KLelong/smartmeter-p1-v1/Software/sm-serial.h

/*
 * sm-serial.h
 * 
 * module to read Smartmeter data from serial port
 */
 
int FindCharInArrayRev(char array[], char c, int len) {
  for (int i = len - 1; i >= 0; i--) {
    if (array[i] == c) {
      return i;
    }
  }
  return -1;
}

long getValidVal(long valNew, long valOld, long maxDiffer)
{
  //check if the incoming value is valid
      if(valOld > 0 && ((valNew - valOld > maxDiffer) && (valOld - valNew > maxDiffer)))
        return valOld;
      return valNew;
}

bool isNumber(char* res, int len) {
  for (int i = 0; i < len; i++) {
    if (((res[i] < '0') || (res[i] > '9'))  && (res[i] != '.' && res[i] != 0)) {
      return false;
    }
  }
  return true;
} 

float getGasValue(char* buffer, int maxlen) {
  int s = FindCharInArrayRev(buffer, '(', maxlen - 2);
  if (s < 8) return 0;
  if (s > 32) s = 32;
  int l = FindCharInArrayRev(buffer, '*', maxlen - 2) - s - 1;
  if (l < 4) return 0;
  if (l > 12) return 0;
  char res[16];
  memset(res, 0, sizeof(res));

  if (strncpy(res, buffer + s + 1, l)) {
    if (isNumber(res, l)) {
      return (atof(res));
    }
  }
  return 0;
}

long getValue(char* buffer, int maxlen) {
  int s = FindCharInArrayRev(buffer, '(', maxlen - 2);
  if (s < 8) return 0;
  if (s > 32) s = 32;
  int l = FindCharInArrayRev(buffer, '*', maxlen - 2) - s - 1;
  if (l < 4) return 0;
  if (l > 12) return 0;
  char res[16];
  memset(res, 0, sizeof(res));

  if (strncpy(res, buffer + s + 1, l)) {
    if (isNumber(res, l)) {
      return (1000 * atof(res));
    }
  }
  return 0;
}

bool decodeTelegram(int len) {
  //need to check for start
  int startChar = FindCharInArrayRev(telegram, '/', len);
  int endChar = FindCharInArrayRev(telegram, '!', len);
  bool endOfMessage = false;
  if(startChar>=0)
  {
    if(outputOnSerial)
    {
      for(int cnt=startChar; cnt<len-startChar;cnt++)
        Serial.print(telegram[cnt]);
    }
  }
  else if(endChar>=0)
  {
    endOfMessage = true;
    if(outputOnSerial)
    {
      for(int cnt=0; cnt<len;cnt++)
        Serial.print(telegram[cnt]);
    }
  }
  else
  {
    if(outputOnSerial)
    {
      for(int cnt=0; cnt<len;cnt++)
        Serial.print(telegram[cnt]);
    }
  }

  long val =0;
  long val2=0;
  // 1-0:1.8.1(000992.992*kWh)
  // 1-0:1.8.1 = Elektra verbruik dag tarief (DSMR v4.0)
  if (strncmp(telegram, "1-0:1.8.1", strlen("1-0:1.8.1")) == 0)
    powerConsumptionDay =  getValue(telegram, len);

  // 1-0:1.8.2(000560.157*kWh)
  // 1-0:1.8.2 = Elektra verbruik nacht tarief (DSMR v4.0)
  if (strncmp(telegram, "1-0:1.8.2", strlen("1-0:1.8.2")) == 0)
    powerConsumptionNight = getValue(telegram, len);


  // 1-0:2.8.1(000348.890*kWh)
  // 1-0:2.8.1 = Elektra injectie dag tarief (DSMR v4.0)
  if (strncmp(telegram, "1-0:2.8.1", strlen("1-0:2.8.1")) == 0)
    powerProductionDay = getValue(telegram, len);


  // 1-0:2.8.2(000859.885*kWh)
  // 1-0:2.8.2 = Elektra injectie nacht tarief (DSMR v4.0)
  if (strncmp(telegram, "1-0:2.8.2", strlen("1-0:2.8.2")) == 0)
    powerProductionNight = getValue(telegram, len);


  // 1-0:1.7.0(00.424*kW) Actueel verbruik
  // 1-0:2.7.0(00.000*kW) Actuele teruglevering
  // 1-0:1.7.x = Electricity consumption actual usage (DSMR v4.0)
  if (strncmp(telegram, "1-0:1.7.0", strlen("1-0:1.7.0")) == 0)
    CurrentPowerConsumption = getValue(telegram, len);

  if (strncmp(telegram, "1-0:2.7.0", strlen("1-0:2.7.0")) == 0)
    CurrentPowerProduction = getValue(telegram, len);


  // 0-1:24.2.3(150531200000S)(00811.923*m3)
  if (strncmp(telegram, "0-1:24.2.3", strlen("0-1:24.2.3")) == 0)
    GasConsumption = getGasValue(telegram, len);

  return endOfMessage;
}

void readTelegram() {
  if (Serial.available()) {
    memset(telegram, 0, sizeof(telegram));
    while (Serial.available()) {
      int len = Serial.readBytesUntil('\n', telegram, MAXLINELENGTH);
      telegram[len] = '\n';
      telegram[len+1] = 0;
      yield();
      if(decodeTelegram(len+1))
      {
        TelegramCount+=1;
        // Sometimes a strange value is seen. To remove these all values are reset, so they can be filtered for MQTT
        if (mqtt_server_def && (TelegramCount>=PublishDelay)) {  
         publishP1ToMqtt();
         TelegramCount=0;
         powerConsumptionDay = 0;
         powerConsumptionNight = 0;
         powerProductionDay = 0;
         powerProductionNight = 0;
         GasConsumption = 0.0;
        }
      }
    }
  }
}
