KLelong/smartmeter-p1-v1/Software/sm-OTA.h

/*
 * sm-OTA.h
 * 
 * module to setup OTA
 */
void OTAsetup () {

  ArduinoOTA.setHostname(hostName);
  ArduinoOTA.setPassword(OTAPassword);
  DEBUG_LOG("OTA Password set :");
  DEBUG_LOG(OTAPassword);
  DEBUG_LOG("\n");
  ArduinoOTA.onStart([]() {
    Serial.println("OTA Start");
  });
  ArduinoOTA.onEnd([]() {
    Serial.println("\nEnd");
  });
  ArduinoOTA.onProgress([](unsigned int progress, unsigned int total) {
    Serial.printf("Progress: %u%%\r", (progress / (total / 100)));
  });
  ArduinoOTA.onError([](ota_error_t error) {
    Serial.printf("Error[%u]: ", error);
    if (error == OTA_AUTH_ERROR) Serial.println("Auth Failed");
    else if (error == OTA_BEGIN_ERROR) Serial.println("Begin Failed");
    else if (error == OTA_CONNECT_ERROR) Serial.println("Connect Failed");
    else if (error == OTA_RECEIVE_ERROR) Serial.println("Receive Failed");
    else if (error == OTA_END_ERROR) Serial.println("End Failed");
  });
  ArduinoOTA.begin(); 

}
